RKouchoo/RCJA-Soccer-Dev/RobotMain/PlatFormioTest/PlatFormioTest/case-test.cpp

#include <Arduino.h>

//i have moved to a different IDE thats why this is a cpp file.

#define InfraredSeeker 1   //just a demo variable.

void loop() {

  //so would these work instead of if statements ?

  switch(InfraredSeeker){

  case 1:
  //movement here
  break;

  case 2:
  //movement here
  break;

  case 3:
  //movement here
  break;

  case 4:
  //movement here
  break;

  case 5:
  //movement here
  break;

  //contiue to number 9
    }
}
